MakeMagazinDE/Dixie-Roehre/Konstruktionszeichnungen/Uhr_Gehäuse/04_GehäuseUntenVierkant.PDF

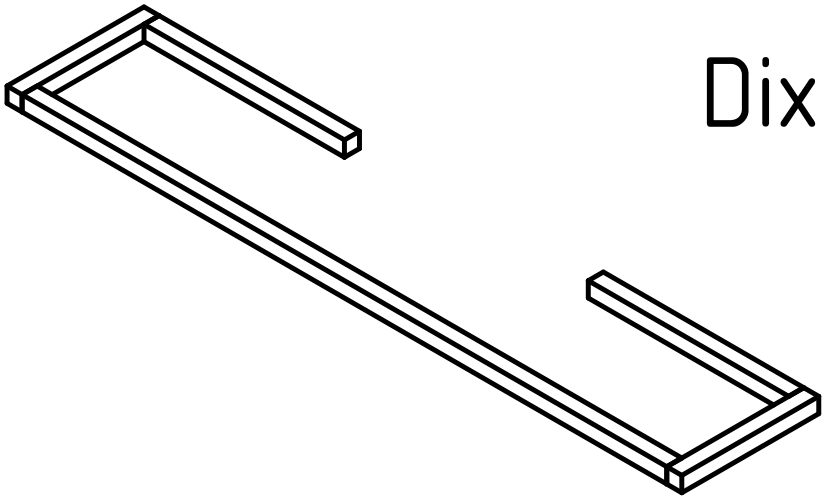
[picture p4: figure]

# Dixie-Uhr Gehäuse

## Vierkant Unten

Material: Vierkant-Holz 9mmx9mm

386,00

9,0

0

120,00

9,0

0

82,00

9,0

0

Vierkant Vorne

### 1 Stück

Vierkant Hinten

### 2 Stück

Vierkant Seite

### 2 Stück
