MakeMagazinDE/Dixie-Roehre/Konstruktionszeichnungen/Uhr_Gehäuse/09_GehäuseObenVierkant.PDF

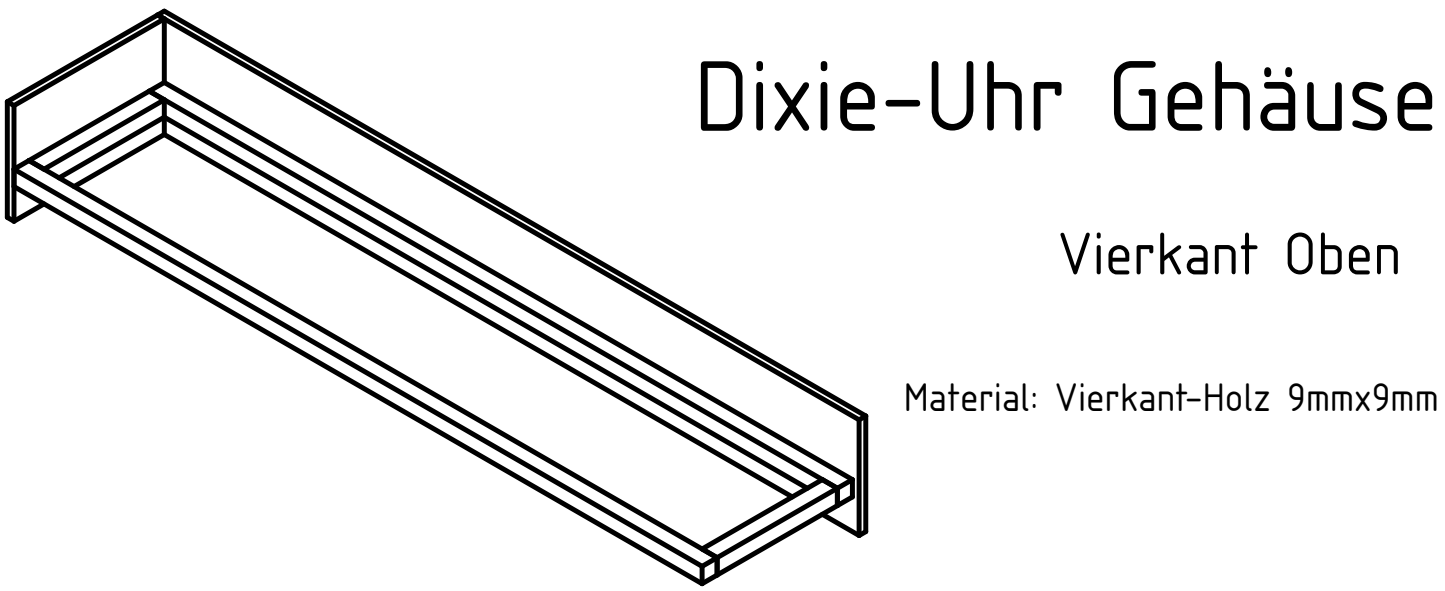
[picture p5: figure]
Dixie-Uhr Gehäuse; Vierkant Oben; Material: Vierkant-Holz 9mmx9mm

412,00

9,0

0

72,00

9,0

0

3

3,0

0

Vierkant
Vorne/Hinten

### 2 Stück

Vierkant Seite

### 2 Stück

Abstand zum kleben der Vierkant-Hölzer:
Oberkante der Platten zu Oberkante der Vierkant-Hölzer
