MakeMagazinDE/Dixie-Roehre/Konstruktionszeichnungen/Uhr_Gehäuse/01_GehäuseÜbersicht.PDF

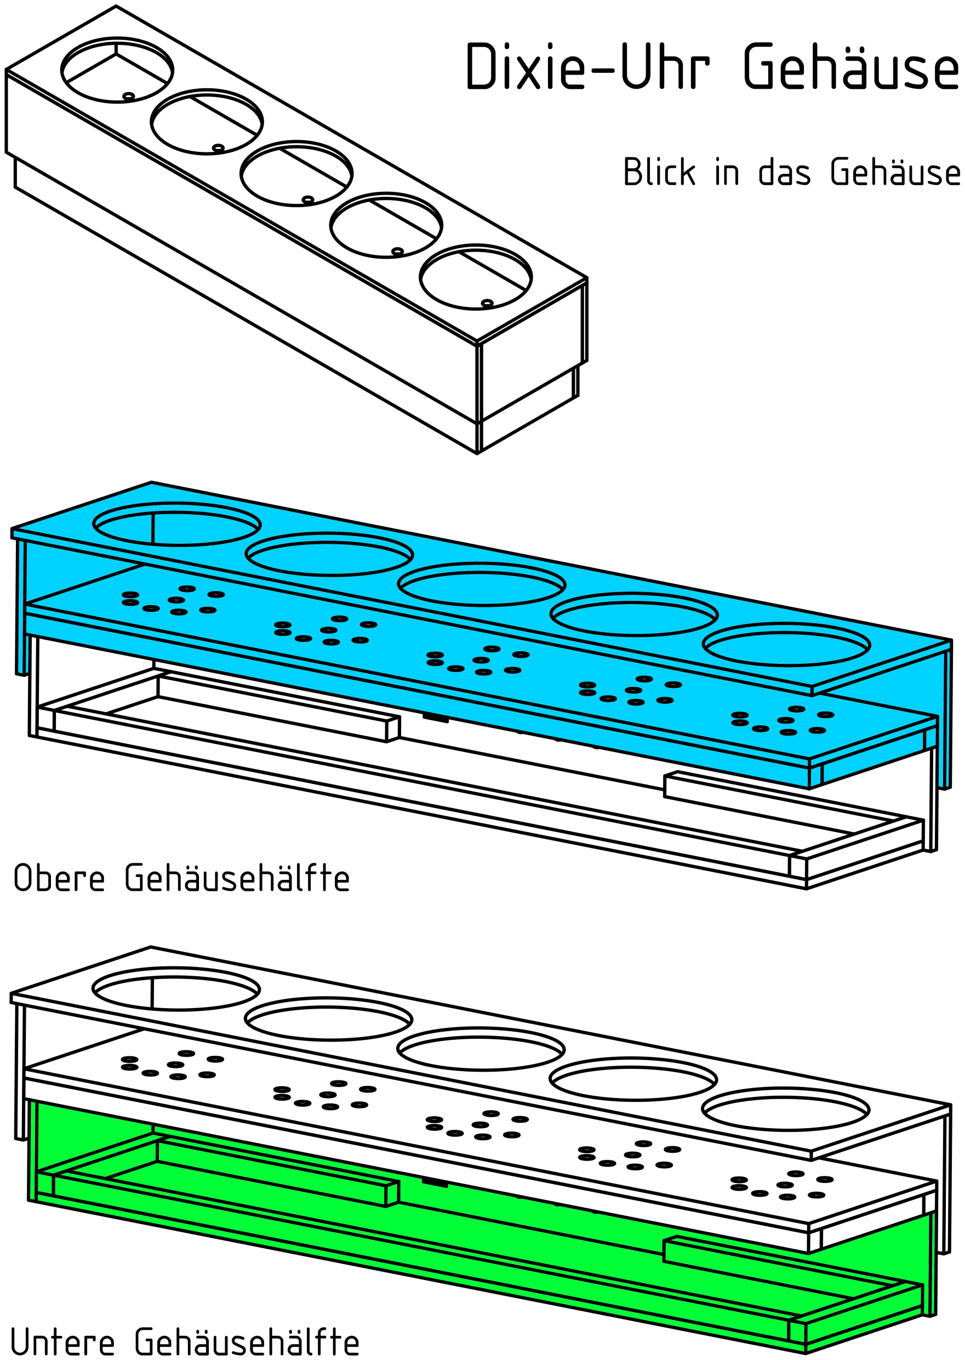
[picture p6: page 1]
