MakeMagazinDE/Dixie-Roehre/Software/SD_Card_Pictures/0.bmp

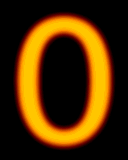
Software/SD_Card_Pictures/0.bmp
