MakeMagazinDE/Dixie-Roehre/Software/SD_Card_Pictures/1.bmp

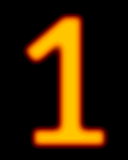
Software/SD_Card_Pictures/1.bmp
