MakeMagazinDE/Dixie-Roehre/Software/SD_Card_Pictures/2.bmp

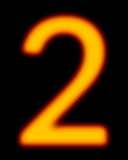
Software/SD_Card_Pictures/2.bmp
