MakeMagazinDE/Dixie-Roehre/Software/SD_Card_Pictures/3.bmp

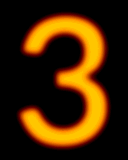
Software/SD_Card_Pictures/3.bmp
