MakeMagazinDE/Dixie-Roehre/Software/SD_Card_Pictures/4.bmp

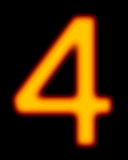
Software/SD_Card_Pictures/4.bmp
