MakeMagazinDE/Dixie-Roehre/Software/SD_Card_Pictures/5.bmp

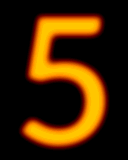
Software/SD_Card_Pictures/5.bmp
