MakeMagazinDE/Dixie-Roehre/Software/SD_Card_Pictures/6.bmp

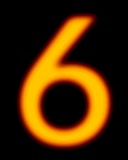
Software/SD_Card_Pictures/6.bmp
