MakeMagazinDE/Dixie-Roehre/Software/SD_Card_Pictures/7.bmp

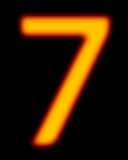
Software/SD_Card_Pictures/7.bmp
