MakeMagazinDE/Dixie-Roehre/Software/SD_Card_Pictures/8.bmp

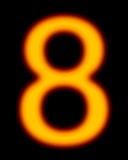
Software/SD_Card_Pictures/8.bmp
