MakeMagazinDE/Dixie-Roehre/Software/SD_Card_Pictures/9.bmp

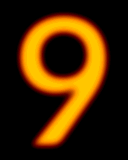
Software/SD_Card_Pictures/9.bmp
