MakeMagazinDE/Dixie-Roehre/Konstruktionszeichnungen/Uhr_Gehäuse/02_GehäuseUntenPlatten.PDF

# Dixie-Uhr Gehäuse

## Unterer Teil: Platten

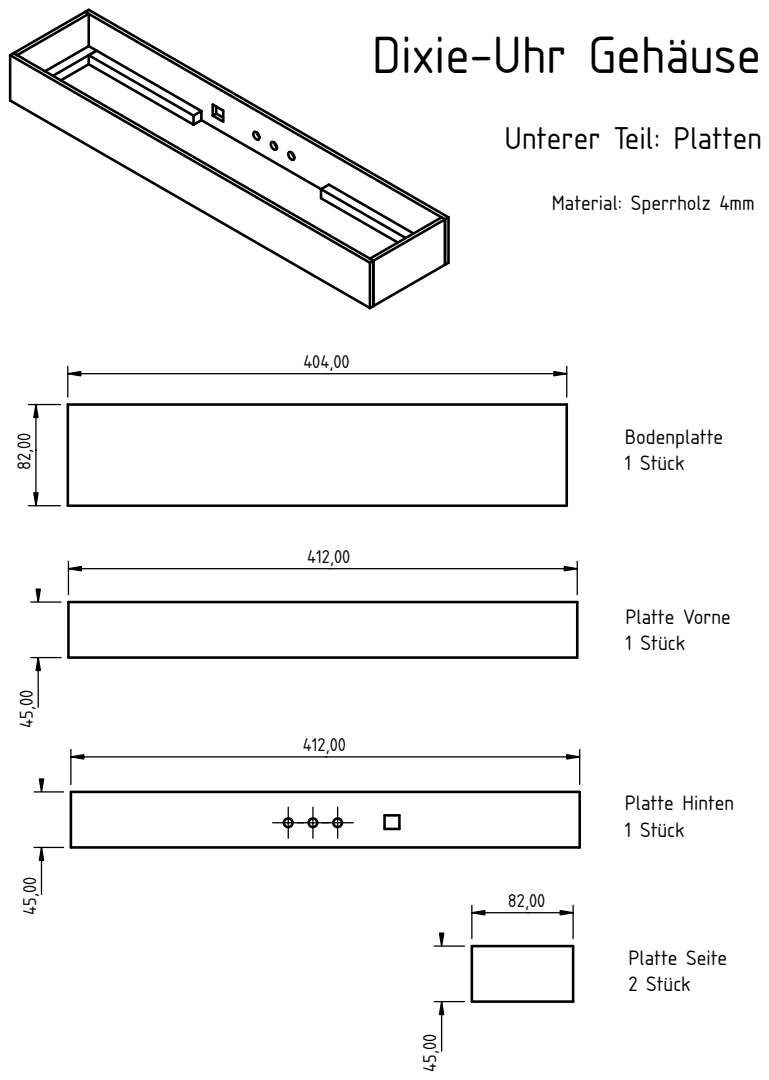
[picture p22: page 1]
Bodenplatte 1 Stück; Material: Sperrholz 4mm; Platte Vorne 1 Stück; Platte Hinten 1 Stück; Platte Seite 2 Stück
