MakeMagazinDE/Dixie-Roehre/Konstruktionszeichnungen/Uhr_Gehäuse/03_GehäuseUntenPlatteHinten.PDF

# Dixie-Uhr Gehäuse

# Unterer Teil: Platte Hinten

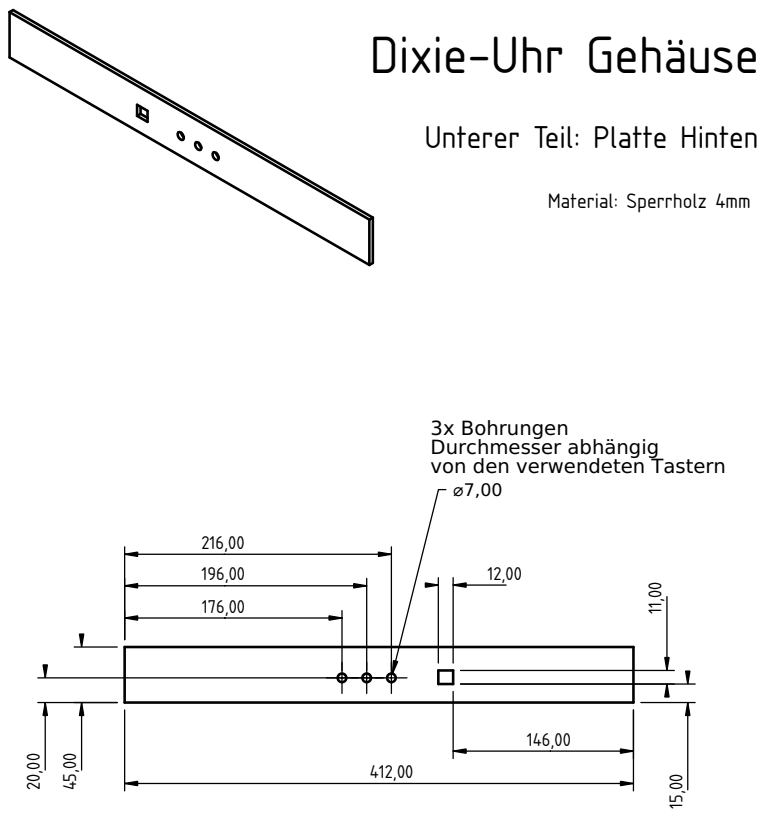
[picture p23: page 1]
Material: Sperrholz 4mm

3x Bohrungen
Durchmesser abhängig
von den verwendeten Tastern
