MakeMagazinDE/Dixie-Roehre/Konstruktionszeichnungen/Uhr_Gehäuse/05_GehäuseObenPlatten.PDF

# Dixie-Uhr Gehäuse

## Oberer Teil: Platten

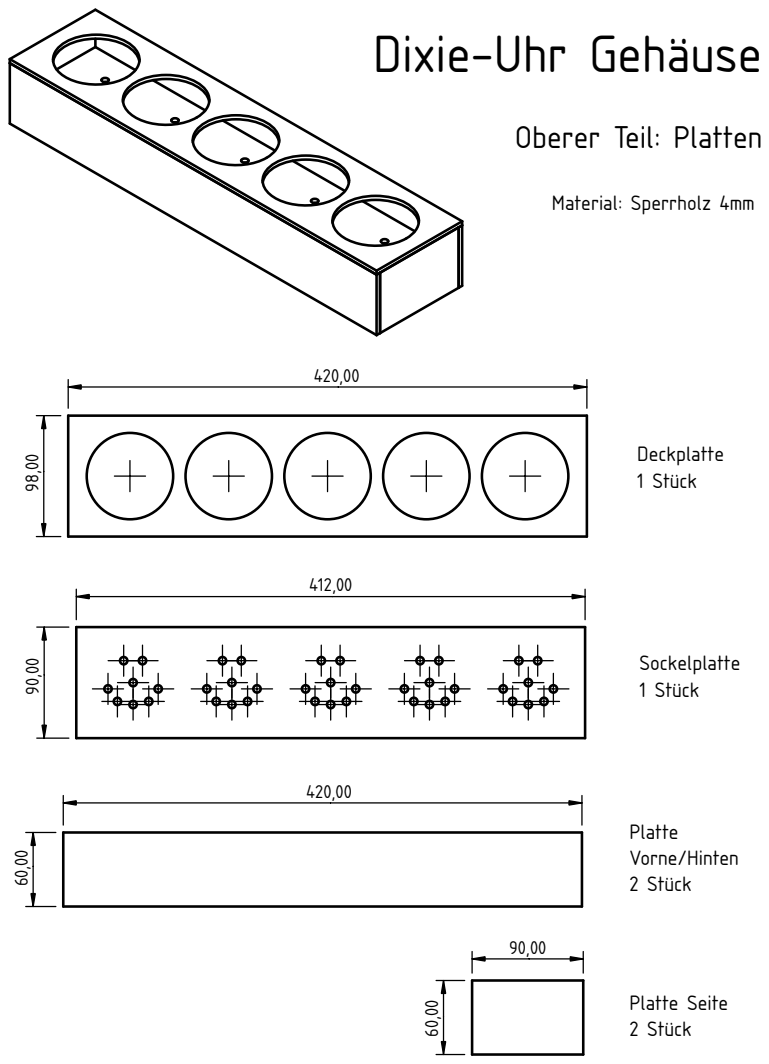
[picture p24: page 1]
Material: Sperrholz 4mm; Deckplatte 1 Stück; Sockelplatte 1 Stück; Platte Vorne/Hinten 2 Stück; Platte Seite 2 Stück
