MakeMagazinDE/Dixie-Roehre/Konstruktionszeichnungen/Uhr_Gehäuse/06_GehäuseObenDeckplatte.PDF

# Dixie-Uhr Gehäuse

# Oberer Teil: Deckplatte

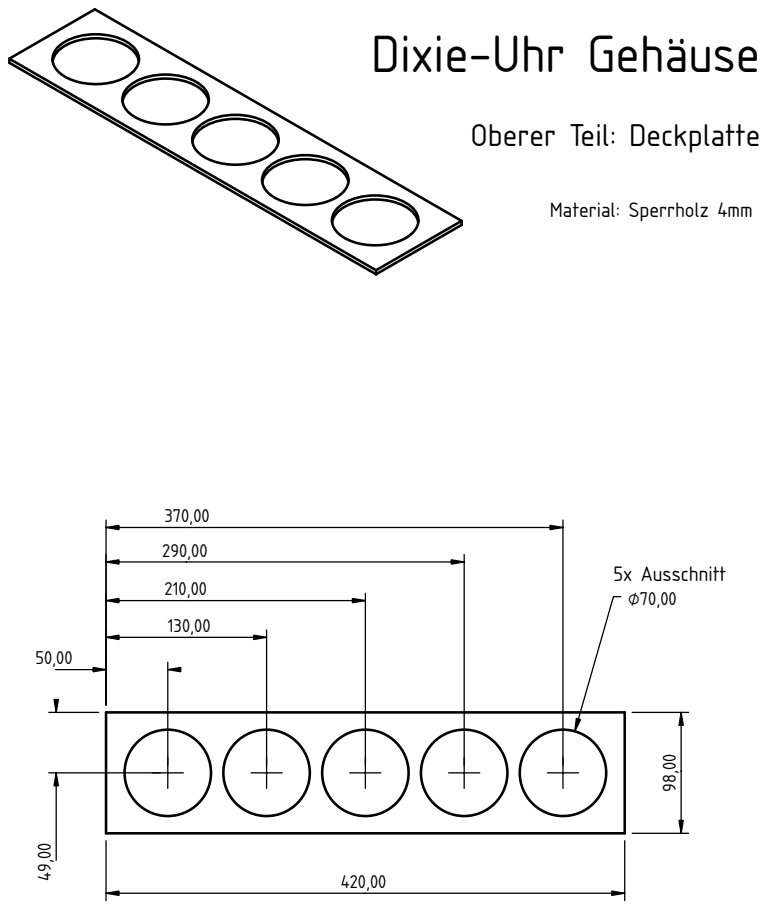
[picture p25: page 1]
Material: Sperrholz 4mm; 5x Ausschnitt
