MakeMagazinDE/Dixie-Roehre/Konstruktionszeichnungen/Uhr_Gehäuse/08_GehäuseObenSockelplatte.PDF

# Dixie-Uhr Gehäuse

# Oberer Teil: Sockelplatte

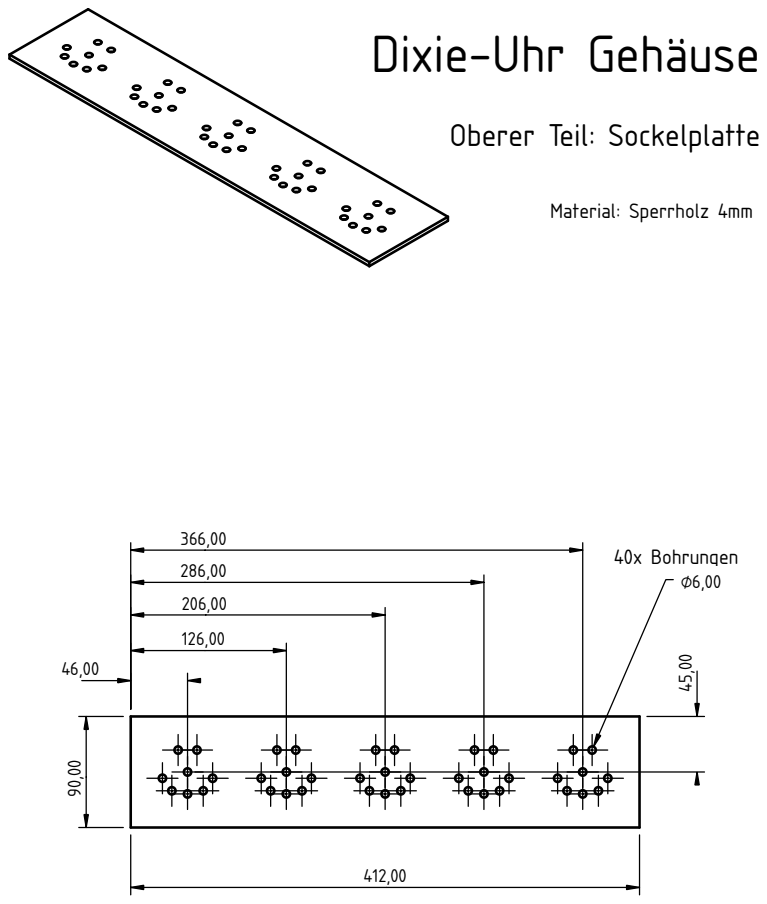
[picture p26: page 1]
Material: Sperrholz 4mm; 40x Bohrungen
