MakeMagazinDE/Dixie-Roehre/Konstruktionszeichnungen/Uhr_Gehäuse/07_GehäuseObenSockelBohrungen.PDF

# Dixie-Uhr Gehäuse

## Oberer Teil: Sockel-Bohrungen

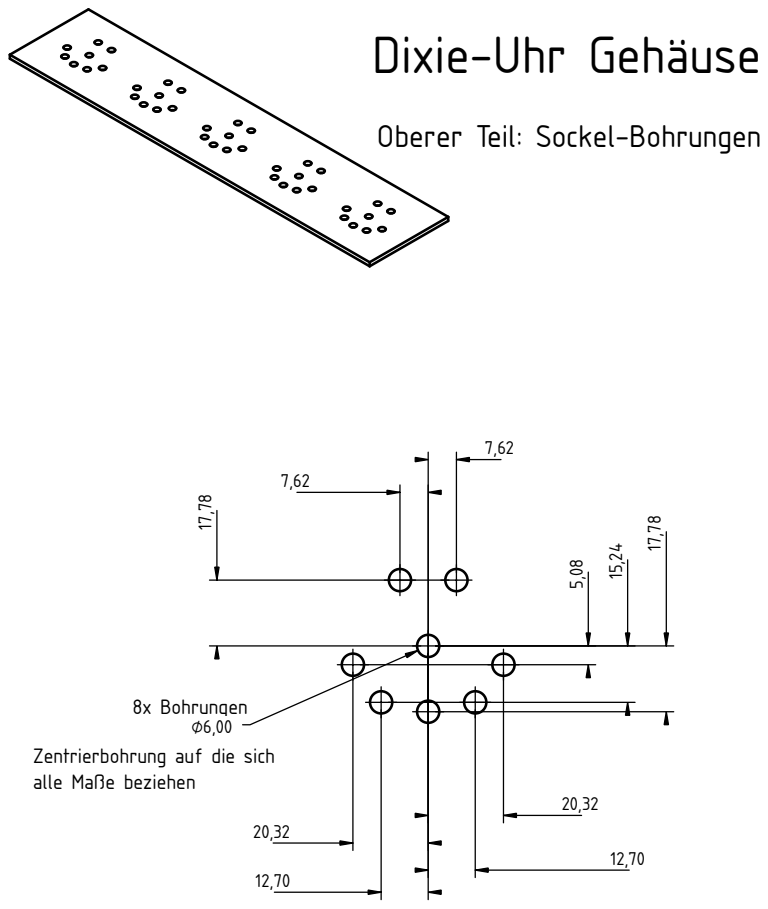
[picture p34: page 1]
8x Bohrungen

Zentrierbohrung auf die sich
alle Maße beziehen
